joshuawong06/Wilkinson-Divider/Images/VNA results/2067_S32.jpg

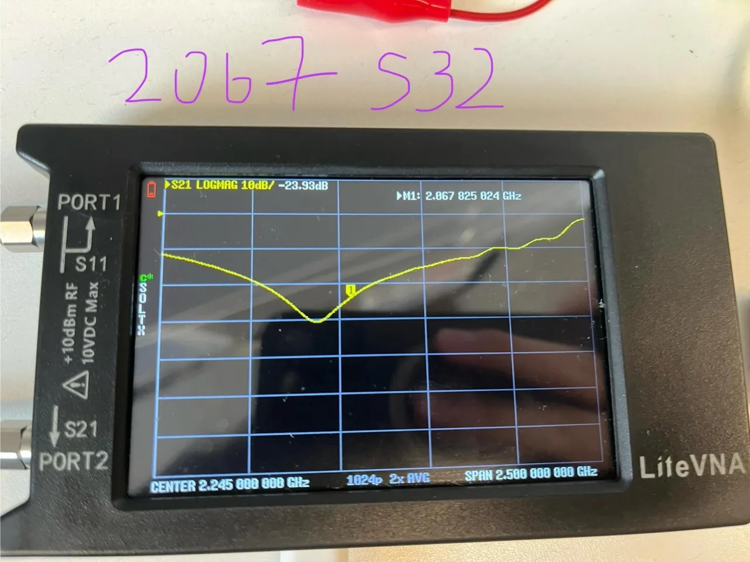
Images/VNA results/2067_S32.jpg
