joshuawong06/Wilkinson-Divider/Images/VNA results/2067_S33.jpg

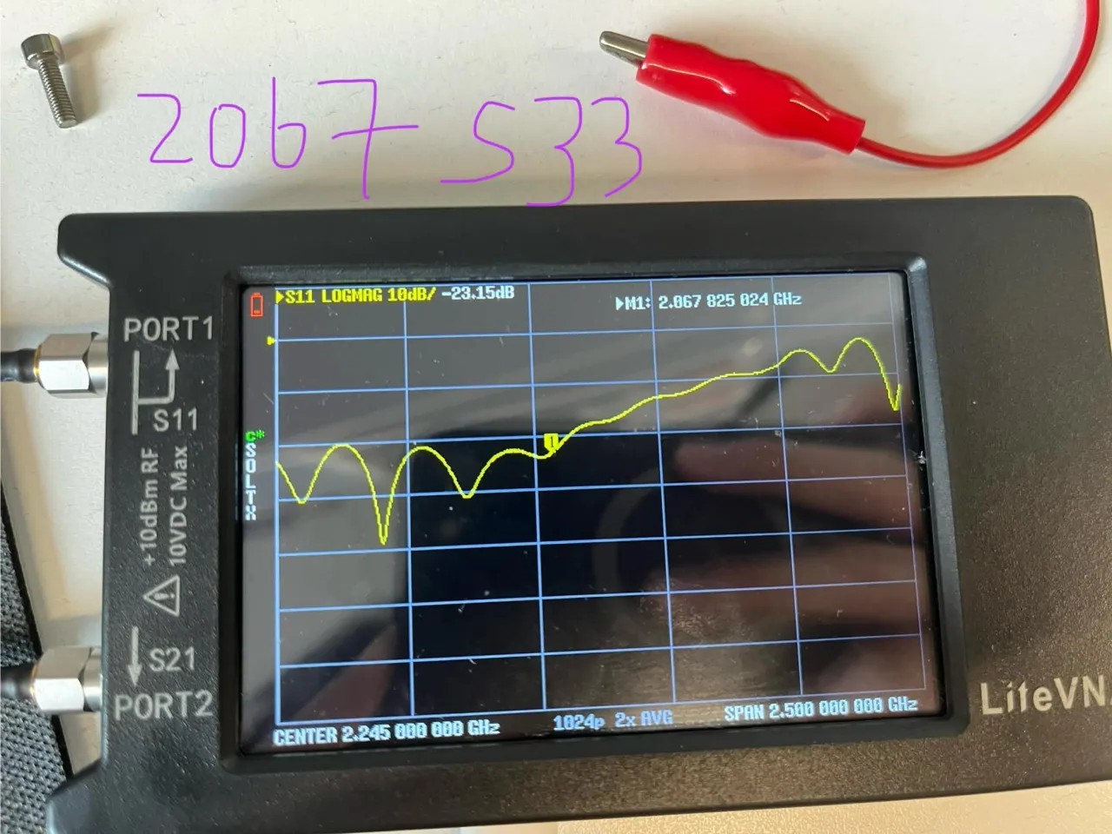
Images/VNA results/2067_S33.jpg
