joshuawong06/Wilkinson-Divider/Images/VNA results/2245_S11.jpg

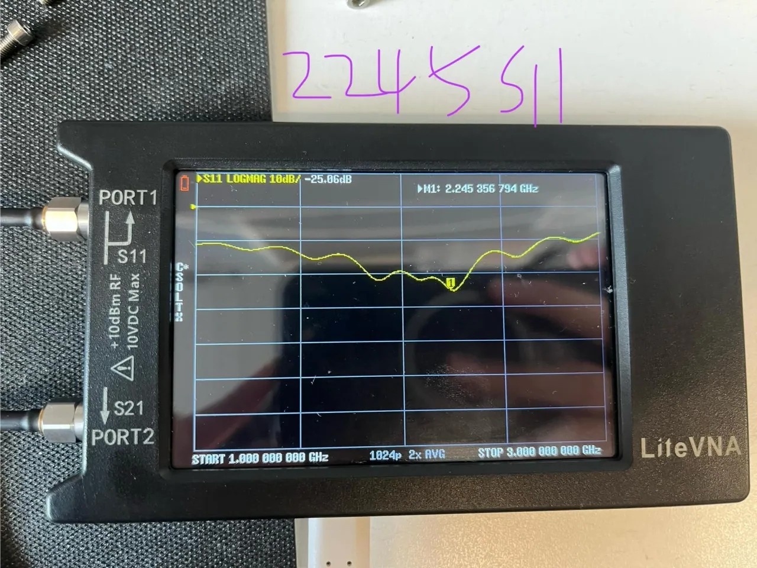
Images/VNA results/2245_S11.jpg
