joshuawong06/Wilkinson-Divider/Images/VNA results/2245_S23.jpg

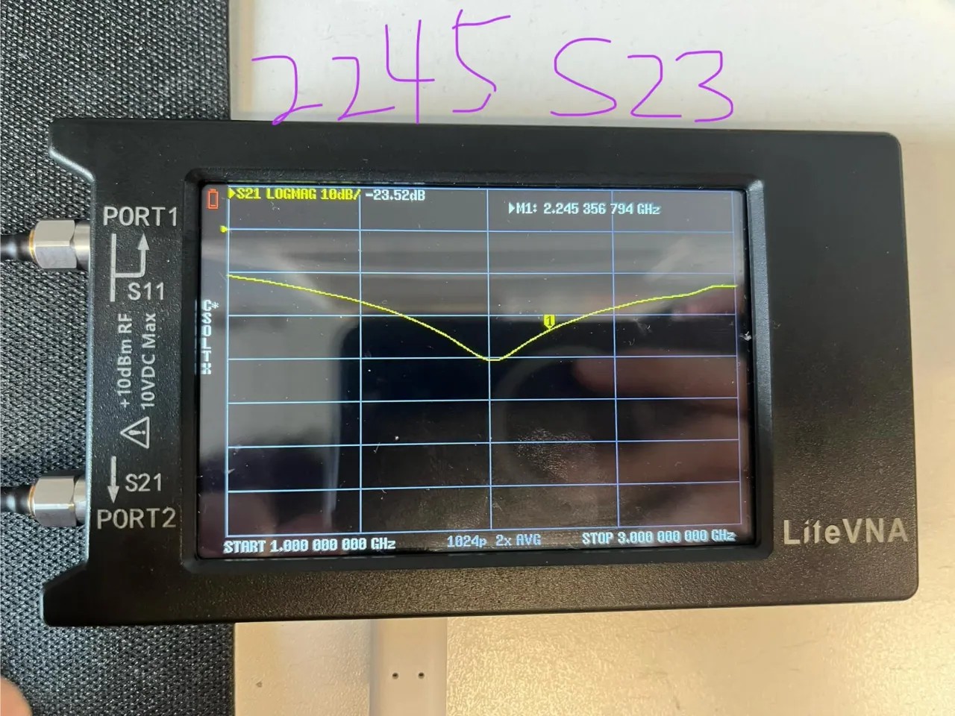
Images/VNA results/2245_S23.jpg
